xionluhnis/ornithopter/hardware/dcboard/outline2.png

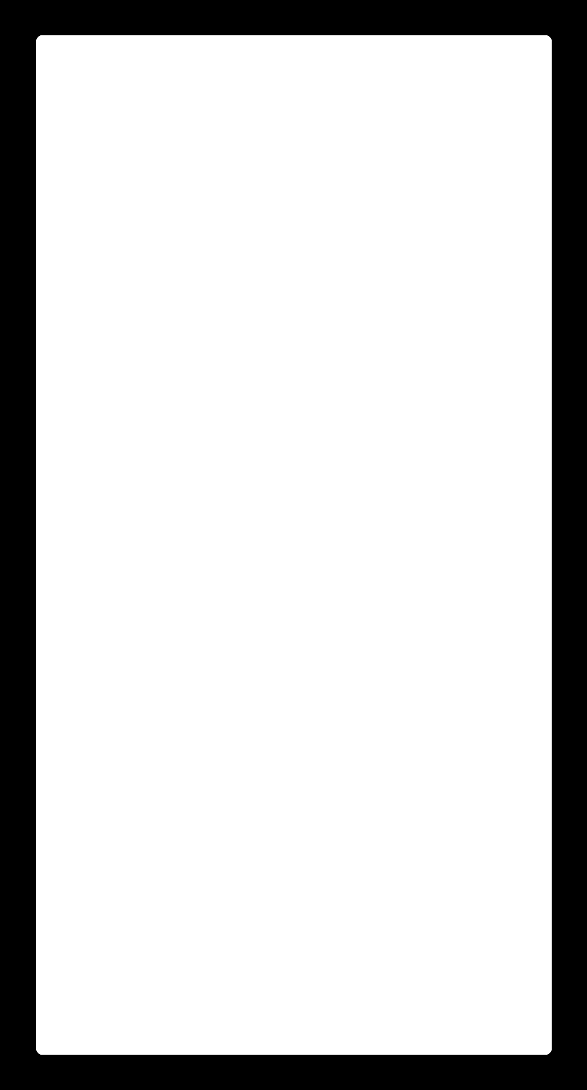
hardware/dcboard/outline2.png
