xionluhnis/ornithopter/hardware/dcboard/trace2.png

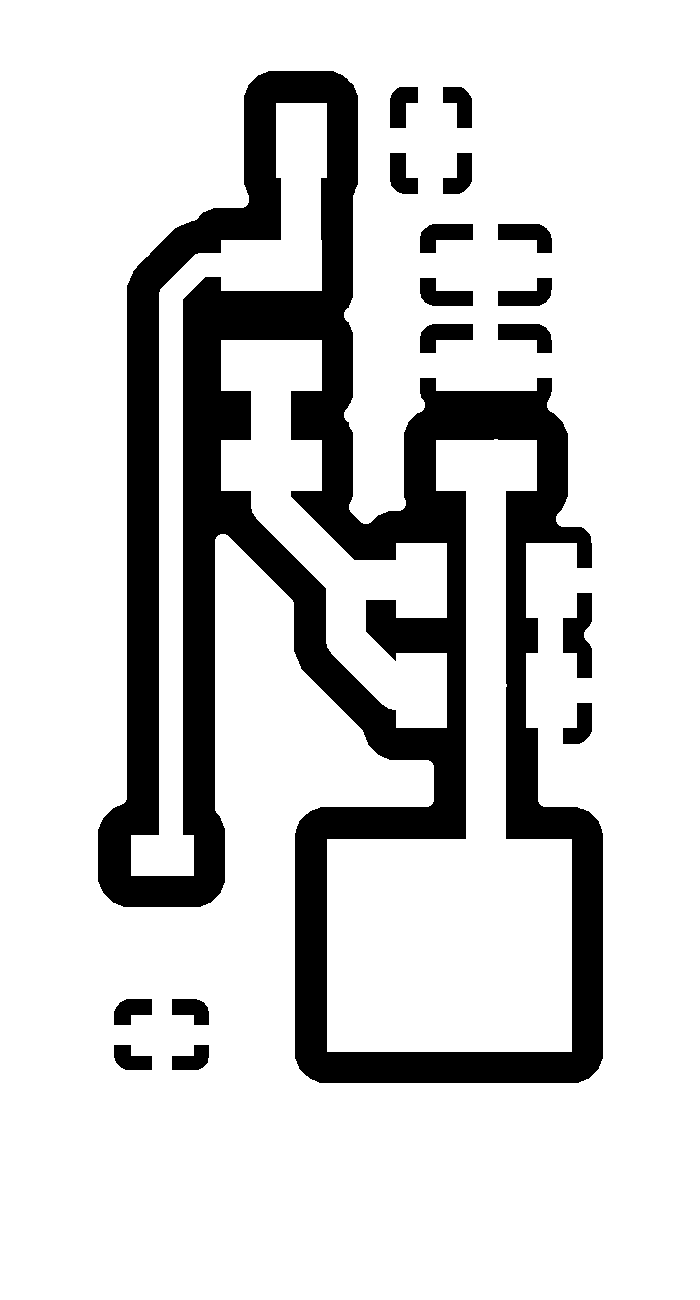
hardware/dcboard/trace2.png
