xionluhnis/ornithopter/hardware/lightboard/board.png

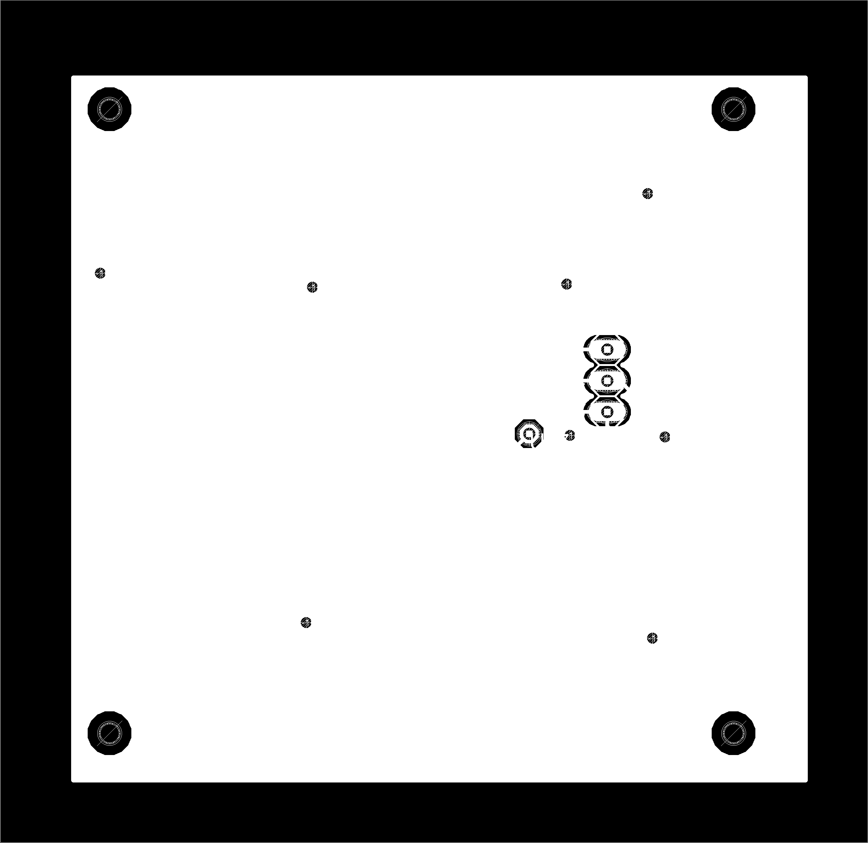
hardware/lightboard/board.png
