xionluhnis/ornithopter/hardware/lightboard/drill.png

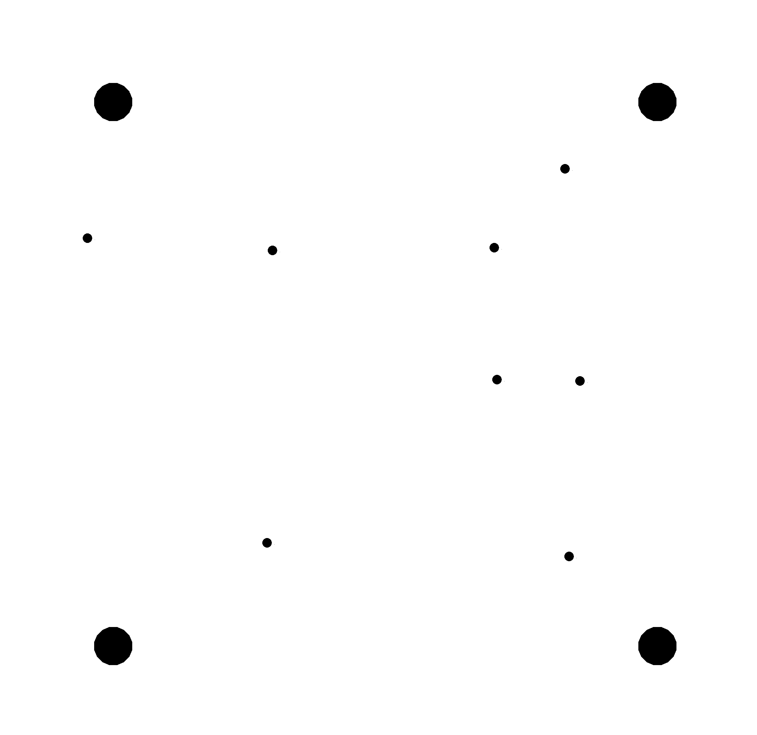
hardware/lightboard/drill.png
