xionluhnis/ornithopter/hardware/lightboard/trace.png

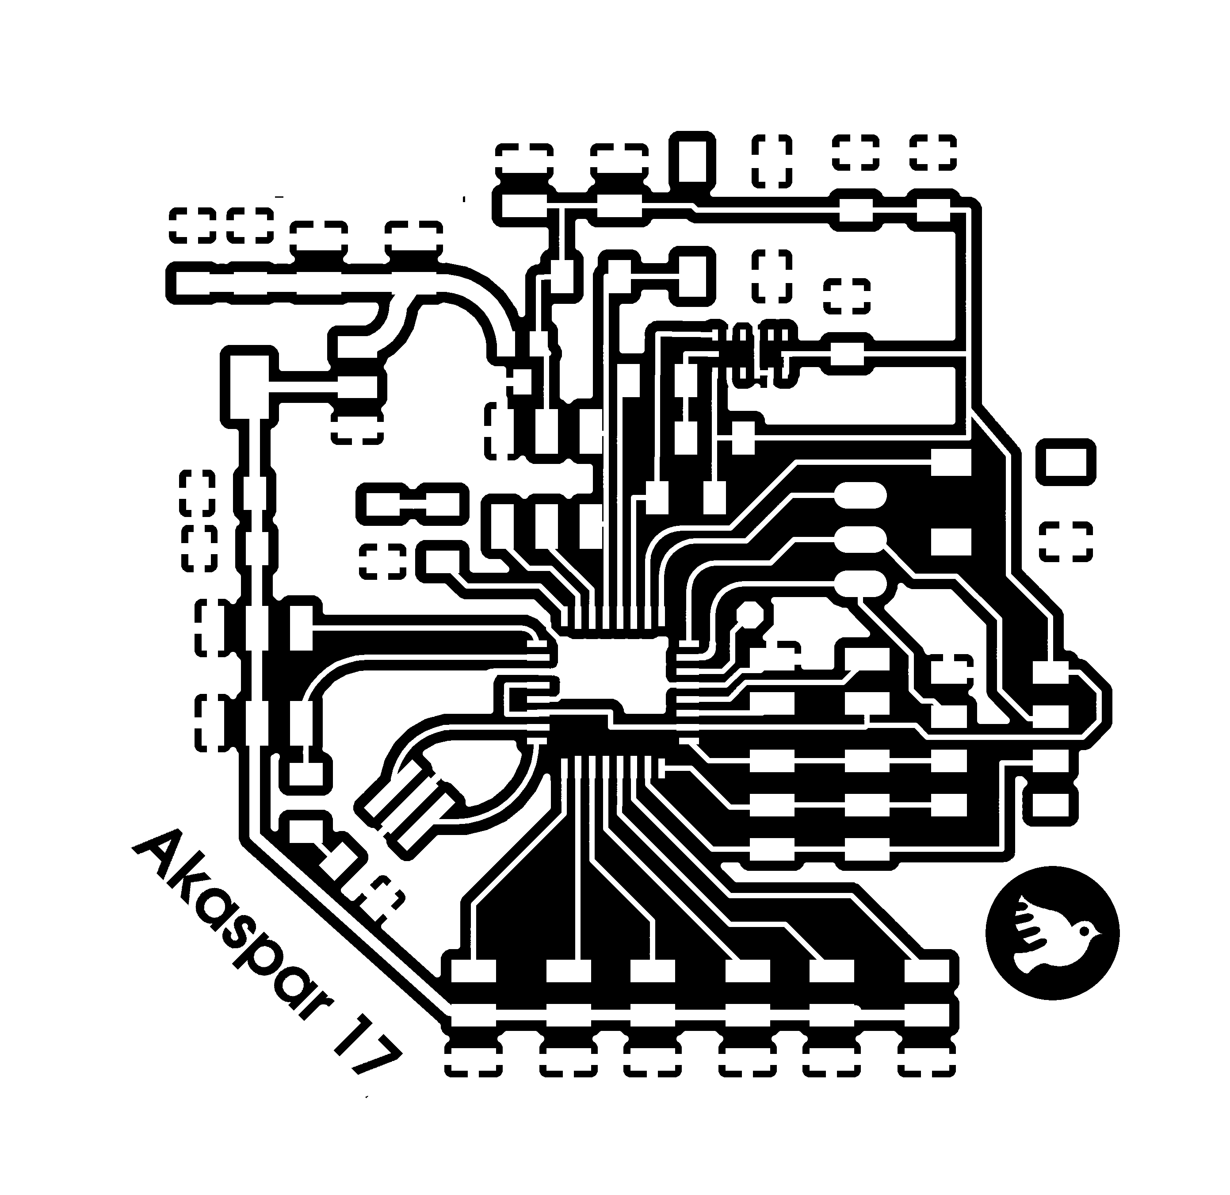
hardware/lightboard/trace.png
