xionluhnis/ornithopter/hardware/lightboard/traceb.png

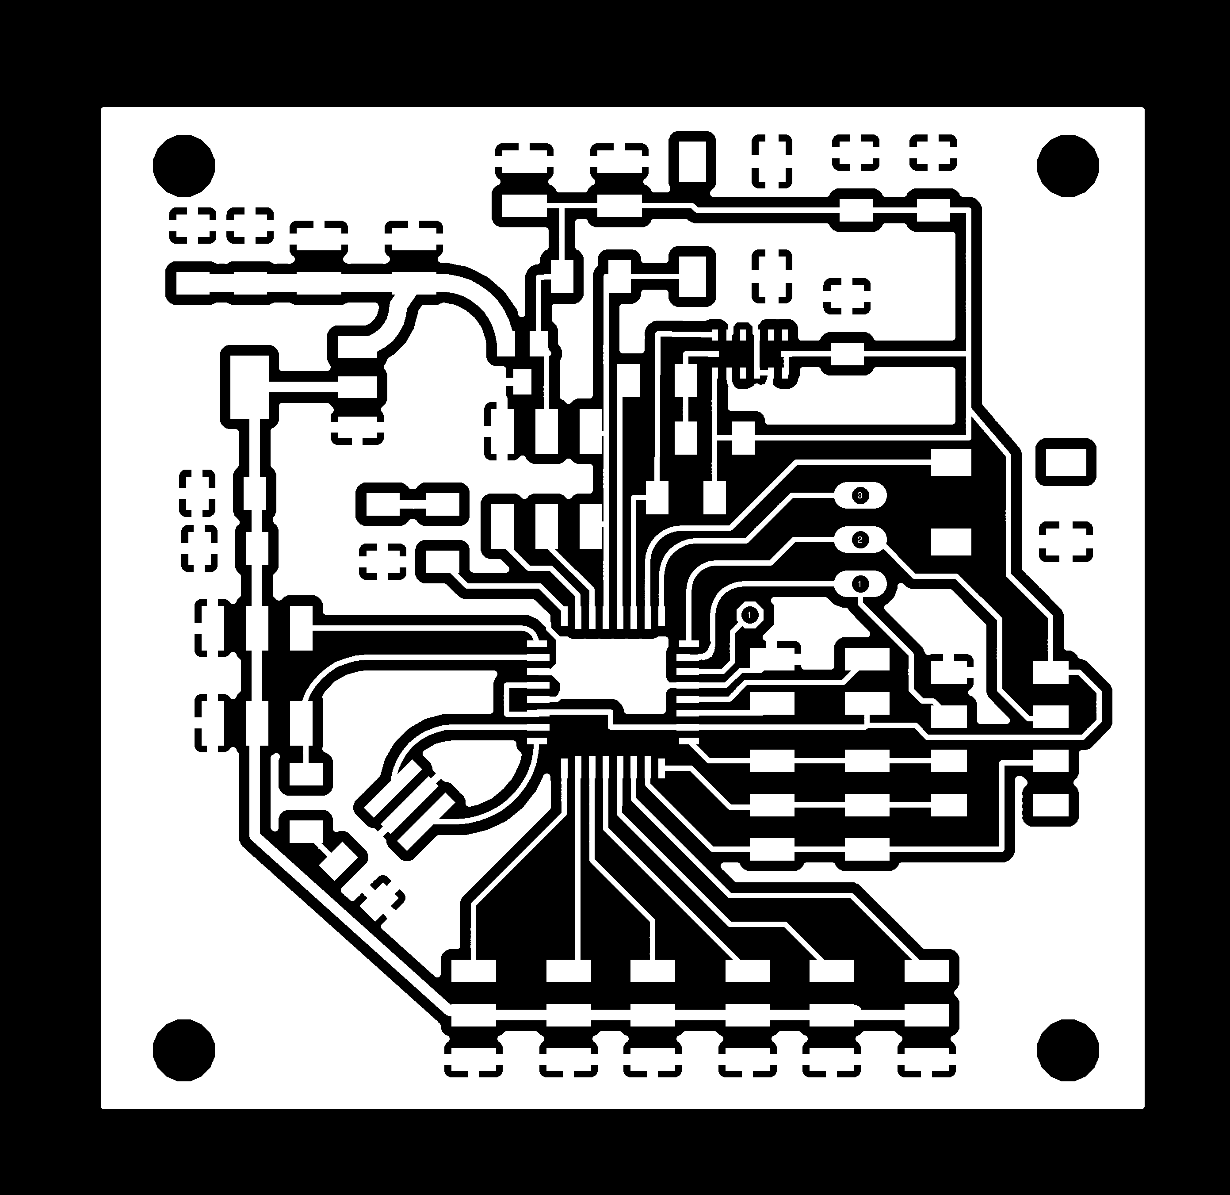
hardware/lightboard/traceb.png
